BoujeeEnjinia1701/twinkit/cad/drawings/TWK-DWG-001.pdf

CONCEPT, NOT FOR FABRICATION | TwinKit · github.com/BoujeeEnjinia1701/twinkit

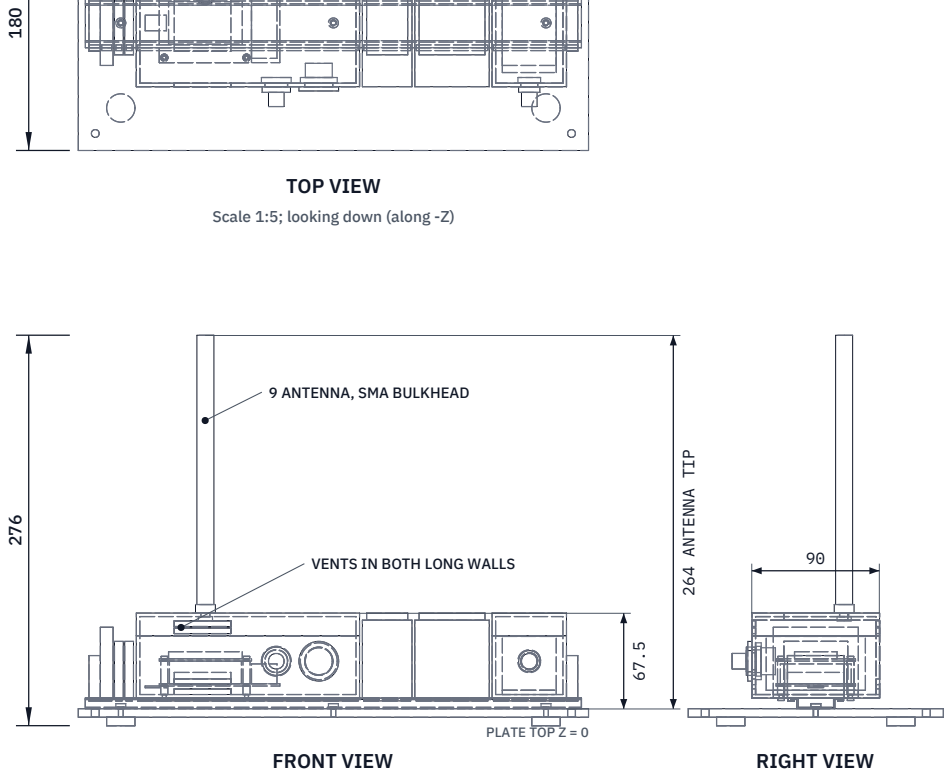
[picture p42: figure]
FRONT VIEW; TOP VIEW; Scale 1:5; looking down (along -Z); RIGHT VIEW; 264 ANTENNA TIP; 9 ANTENNA, SMA BULKHEAD; VENTS IN BOTH LONG WALLS; PLATE TOP Z = 0

Scale 1:5; looking at the front (along +Y)

Scale 1:5; looking at the right side (along -X)

360

331 RAIL USED (18.9 MODULES)

157.5 (9 MODULES)

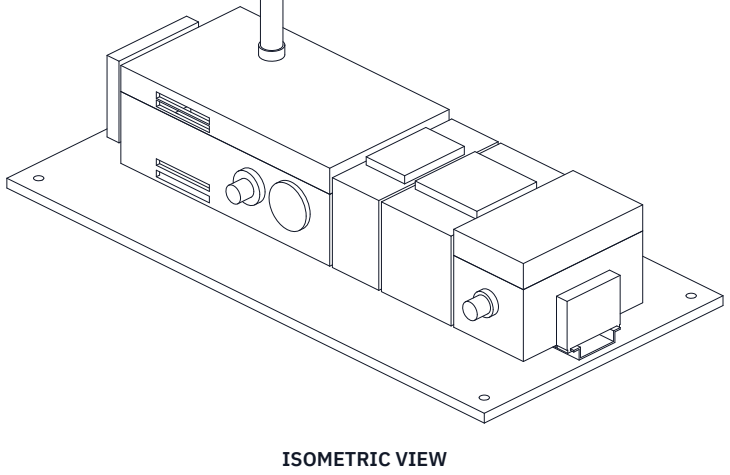
[picture p43: figure]
ISOMETRIC VIEW

Not to scale; seen from the front right and above, about 30 deg elevation

MAIN DIMENSIONS AND INTERFACES (MM)
TS35 x 7.5 rail, 350 long, on 3 M4 screws; module pitch 17.5
13 terminals, fuse | 3, 4 enclosure 9 mod | 10 DC-DC 2 mod | 11 UPS 3 mod
17 battery box 3 mod holding 12 pack (12.8 V, 1.5 Ah) | 18 end stops
Enclosure 157.5 x 90 x 60 above the rail; top 67.5 above the plate
Vents 640 mm2 low and high, 42 apart (TWK-CAL-001 F)
5 board 85 x 56 on 6 standoffs; 7 HAT on 16 standoffs
20 RJ45 coupler and cable glands in the -Y walls; 9 to 30 V DC in Plate 360 x 180 x 6 aluminium; omit in a cabinet
Third-angle; front view from -Y; X along the rail
REV | DESCRIPTION | DATE | BY
P1 | Preliminary GA for TRL 3 (from cad/src/model.py) | 2026-09-25 | AC
P2 | Layout and labels tidied | 2026-09-25 | AC
P3 | Constructable design: vents in long walls, battery box, end stops, fixings (TWK-DDR-003) | 2026-10-02 | AC
TWINKIT | github.com/BoujeeEnjinia1701/twinkit

## General arrangement, edge gateway

DRAWING NO.
TWK-DWG-001

REV
P3

SHEET
1 of 1

SIZE

## ANSI B

SCALE
1:5

UNITS
mm
PROJECTION | DATE
2026-10-02

DRAWN
Amish Chadha

MATERIAL / NOTES
Bought-in DIN modules per bom/bom.csv. PRELIMINARY, NOT FOR FABRICATION
Licensed CERN-OHL-S-2.0 · Design Molecule Lab · designmolecule.com | Generated from cad/src; do not edit by hand
