BoujeeEnjinia1701/twinkit/cad/drawings/TWK-DWG-101.pdf

### BUILD PLAN SKETCH, PLAN NOT YET BUILT TwinKit · github.com/BoujeeEnjinia1701/twinkit

FRONT VIEW
Scale 1:5; looking at the front (along +Y)

TOP VIEW
Scale 1:5; looking down (along -Z)

RIGHT VIEW
Scale 1:5; looking at the right side (along -X)

360

180 6

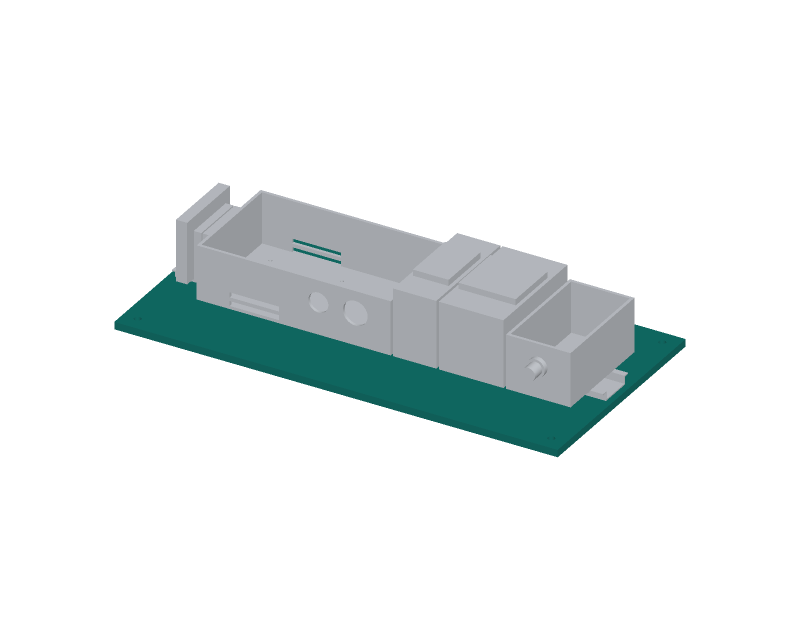
[picture p44: figure]

WHERE IT GOES
This part in colour, its neighbours in grey

HOW TO MAKE IT AND HOW IT FITS
Blank 360 x 180 x 6 mm. Cut square, file the edges, round the corners to about 3 mm. Scribe a centre line along the long side. Rail holes: three on the centre line, at the middle and 150 mm
each side of it. Drill 3.3 mm right through and tap M4.
Corner holes: four 5.5 mm holes, 12 mm in from each long and short edge, for screwing the plate to a wall or cabinet later.
Deburr every hole on both faces.
Underneath: four stick-on rubber feet, 20 mm across, centred
150 mm each side of the middle and 60 mm each side of the centre line. Fit: the rail lies on the centre line, held by three M4 x 6 mm
pan-head screws through its base into the tapped holes.
Check: an M4 screw runs into each hole by hand; the plate rocks
on none of its feet on a flat bench.
REV | DESCRIPTION | DATE | BY
P1 | Making sketch for the prototype build plan | 2026-10-02 | AC
TWINKIT | github.com/BoujeeEnjinia1701/twinkit

## TwinKit bench plate: making sketch

DRAWING NO.
TWK-DWG-101

REV
P1

SHEET
1 of 1

SIZE

## ANSI B

SCALE
1:5

UNITS
mm
PROJECTION | DATE
2026-10-02

DRAWN
Amish Chadha

MATERIAL / NOTES
Aluminium sheet 6 mm, 5083, 6082 or 6061 class
Licensed CERN-OHL-S-2.0 · Design Molecule Lab · designmolecule.com | Generated from cad/src; do not edit by hand
