BoujeeEnjinia1701/twinkit/cad/drawings/TWK-DWG-102.pdf

### BUILD PLAN SKETCH, PLAN NOT YET BUILT TwinKit · github.com/BoujeeEnjinia1701/twinkit

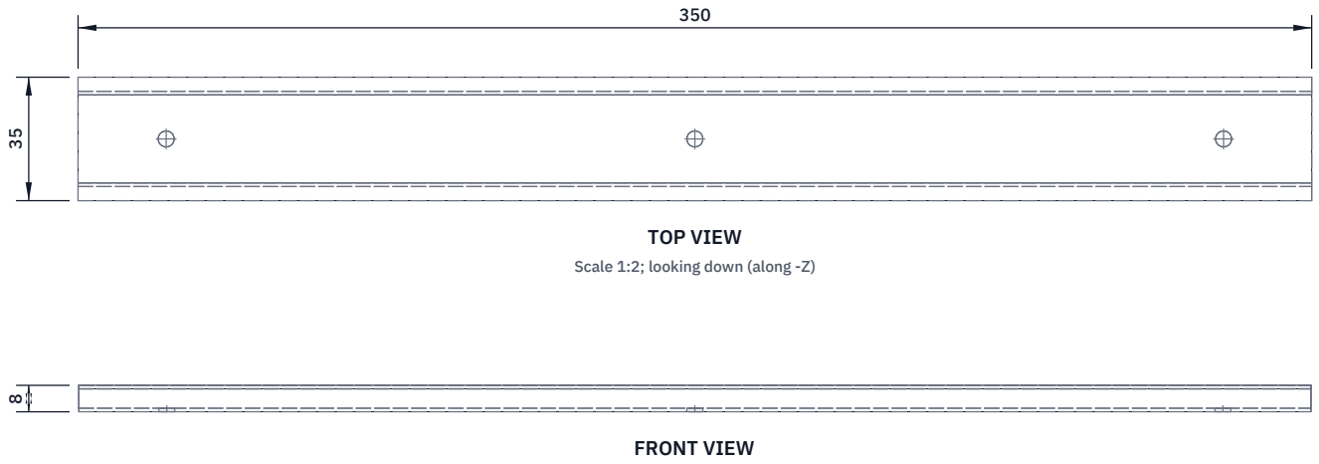
[picture p45: figure]
FRONT VIEW; TOP VIEW; Scale 1:2; looking down (along -Z)

Scale 1:2; looking at the front (along +Y)

RIGHT VIEW
Scale 1:2; looking at the right side (along -X)

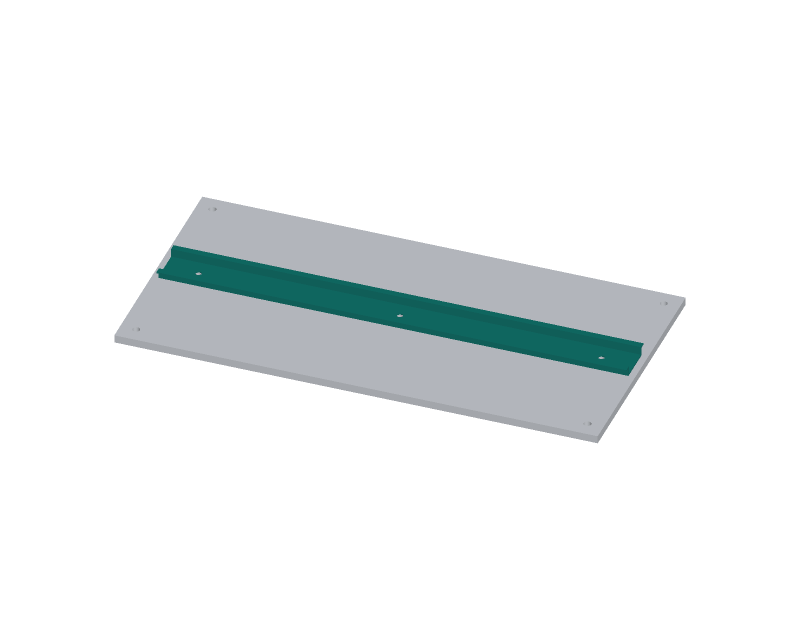
[picture p46: figure]

WHERE IT GOES
This part in colour, its neighbours in grey

HOW TO MAKE IT AND HOW IT FITS
Cut a 350 mm length of TS35 x 7.5 slotted top-hat rail with a hacksaw; file the cut ends square and remove every burr.
The rail is 35 mm wide across its top flanges, 7.5 mm high, with a 27 mm wide base that lies on the plate.
Holes: three, on the rail's centre line, at the middle and 150 mm each side. Where a slot already falls within 3 mm of a mark, use the slot; otherwise drill 4.5 mm through the base.
Fit: lay the rail on the plate's centre line, ends 5 mm in from the plate's short edges. Three M4 x 6 mm pan-head screws, snug. Every module clips over the two top flanges; the screw heads sit 3.9 mm below the modules, so nothing rubs.
Check: the rail lies flat along its length; a module clips on and slides along it from end to end without catching on a screw.
REV | DESCRIPTION | DATE | BY
P1 | Making sketch for the prototype build plan | 2026-10-02 | AC
TWINKIT | github.com/BoujeeEnjinia1701/twinkit

## TwinKit DIN rail: making sketch

DRAWING NO.
TWK-DWG-102

REV
P1

SHEET
1 of 1

SIZE

## ANSI B

SCALE
1:2

UNITS
mm
PROJECTION | DATE
2026-10-02

DRAWN
Amish Chadha

MATERIAL / NOTES
TS35 x 7.5 top-hat rail, slotted, steel or aluminium
Licensed CERN-OHL-S-2.0 · Design Molecule Lab · designmolecule.com | Generated from cad/src; do not edit by hand
