BoujeeEnjinia1701/twinkit/cad/drawings/TWK-DWG-103.pdf

### BUILD PLAN SKETCH, PLAN NOT YET BUILT TwinKit · github.com/BoujeeEnjinia1701/twinkit

FRONT VIEW
Scale 1:2; looking at the front (along +Y)

TOP VIEW
Scale 1:2; looking down (along -Z)

RIGHT VIEW
Scale 1:2; looking at the right side (along -X)

158

90 46

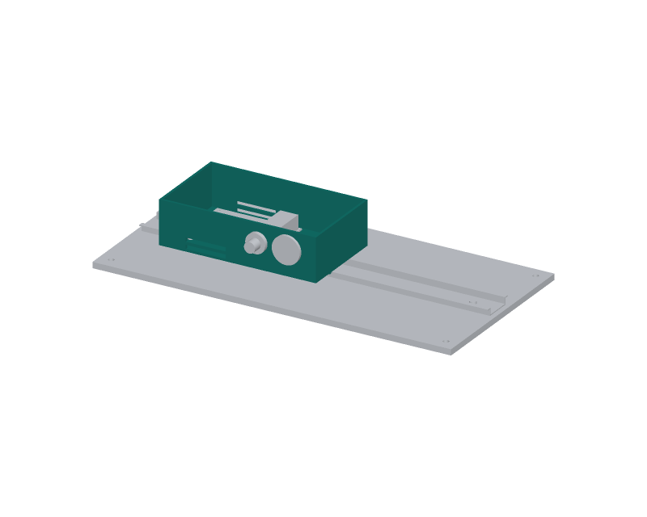
[picture p47: figure]

WHERE IT GOES
This part in colour, its neighbours in grey

HOW TO MAKE IT AND HOW IT FITS
The front is the long wall that will face you on the bench; the antenna sits toward the back. Mark the front before cutting. Vent slots: two slots 40 x 4 mm in each long wall, centred 32 mm left of the middle, 2.5 to 6.5 and 9.5 to 13.5 mm above the outside of the floor. Chain drill 3.5 mm and file to the line.
Front wall, 26 mm above the outside of the floor: a 20 mm hole 50 mm right of the middle (network coupler) and a 16.2 mm hole 20 mm right of the middle (power gland). Step drill, light pressure. Floor: four 2.7 mm holes for the computer: 58 mm apart along the base and 49 mm apart across it, the left pair 59 mm and the right pair 1 mm left of the middle. Use the maker's bosses if it has them. Tape the faces first; no solvents; deburr inside and out.
Check: lay the computer on the floor; its holes line up with yours.
REV | DESCRIPTION | DATE | BY
P1 | Making sketch for the prototype build plan | 2026-10-02 | AC
TWINKIT | github.com/BoujeeEnjinia1701/twinkit

## TwinKit gateway enclosure base: cutting and drilling sketch

DRAWING NO.
TWK-DWG-103

REV
P1

SHEET
1 of 1

SIZE

## ANSI B

SCALE
1:2

UNITS
mm
PROJECTION | DATE
2026-10-02

DRAWN
Amish Chadha

MATERIAL / NOTES
Bought 9-module DIN enclosure base, polycarbonate, 157.5 x 90 x 44 mm
Licensed CERN-OHL-S-2.0 · Design Molecule Lab · designmolecule.com | Generated from cad/src; do not edit by hand
