BoujeeEnjinia1701/twinkit/cad/drawings/TWK-DWG-104.pdf

### BUILD PLAN SKETCH, PLAN NOT YET BUILT TwinKit · github.com/BoujeeEnjinia1701/twinkit

FRONT VIEW
Scale 1:2; looking at the front (along +Y)

TOP VIEW
Scale 1:2; looking down (along -Z)

RIGHT VIEW
Scale 1:2; looking at the right side (along -X)

158

90 16

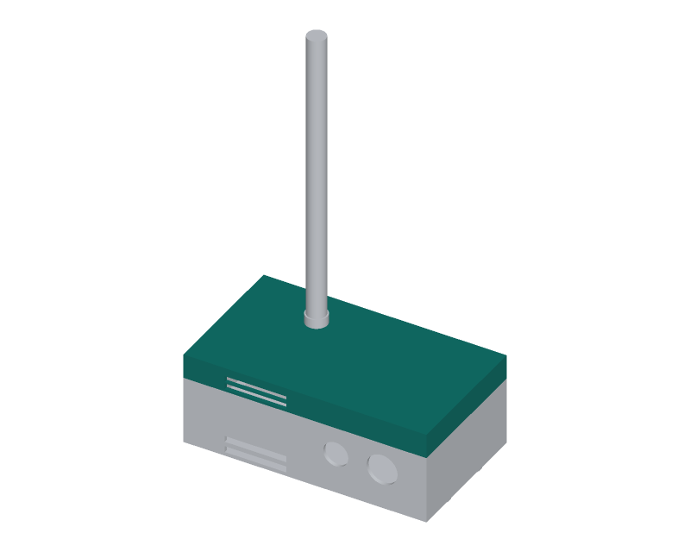
[picture p48: figure]

WHERE IT GOES
This part in colour, its neighbours in grey

HOW TO MAKE IT AND HOW IT FITS
Antenna hole: 6.5 mm through the top, 30 mm left of the middle and 20 mm behind the centre line (toward the back wall).
Pilot 3 mm, then step drill; check the size on the bulkhead's datasheet before the last step.
Vent slots: two slots 40 x 4 mm in each long wall, in line with the base's slots, 1.5 to 5.5 and 6.5 to 10.5 mm above the cover's lower edge. Skip any the maker has already moulded.
Deburr; clean with water and mild soap only.
Fit: the bulkhead goes in from above, flange and washer on the outside, nut inside. The cover then closes onto the base with
the maker's clips or screws.
Check: the bulkhead nut clears the concentrator HAT by 20 mm when the cover is closed.
REV | DESCRIPTION | DATE | BY
P1 | Making sketch for the prototype build plan | 2026-10-02 | AC
TWINKIT | github.com/BoujeeEnjinia1701/twinkit

## TwinKit gateway enclosure cover: drilling sketch

DRAWING NO.
TWK-DWG-104

REV
P1

SHEET
1 of 1

SIZE

## ANSI B

SCALE
1:2

UNITS
mm
PROJECTION | DATE
2026-10-02

DRAWN
Amish Chadha

MATERIAL / NOTES
Bought cover for the 9-module enclosure, clear or tinted polycarbonate
Licensed CERN-OHL-S-2.0 · Design Molecule Lab · designmolecule.com | Generated from cad/src; do not edit by hand
