BoujeeEnjinia1701/twinkit/cad/drawings/TWK-DWG-105.pdf

### BUILD PLAN SKETCH, PLAN NOT YET BUILT TwinKit · github.com/BoujeeEnjinia1701/twinkit

FRONT VIEW
Scale 1:2; looking at the front (along +Y)

TOP VIEW
Scale 1:2; looking down (along -Z)

RIGHT VIEW
Scale 1:2; looking at the right side (along -X)

52

90 46

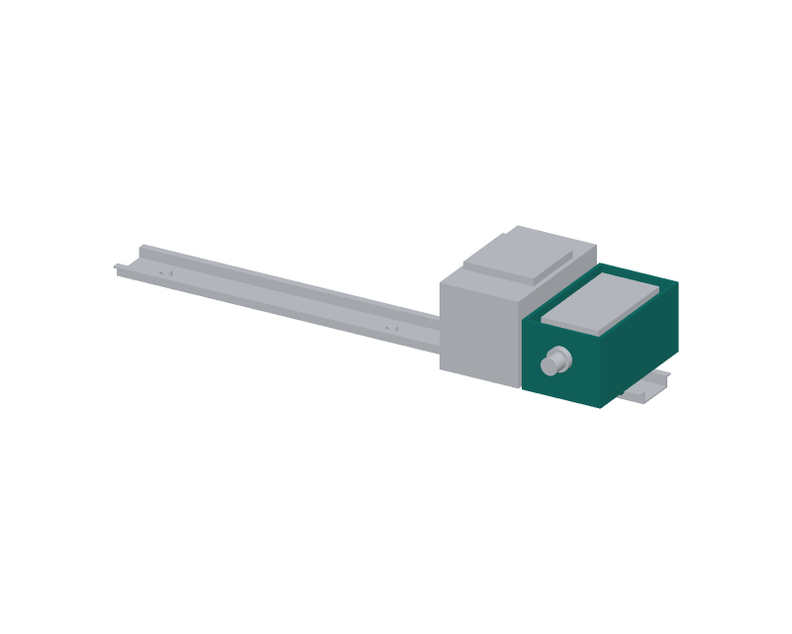
[picture p49: figure]

WHERE IT GOES
This part in colour, its neighbours in grey

HOW TO MAKE IT AND HOW IT FITS
One 12.2 mm hole in the front wall, on the middle of the wall, 26 mm above the outside of the floor, for the M12 gland that
the pack lead passes through. Pilot 3 mm, then step drill.
Deburr inside and out.
Inside: a hook-and-loop pad 38 x 60 mm stuck to the middle of the floor; its mate goes on the pack's underside.
The pack (38 x 70 x 38 mm at most) lies on the pad, long side front to back, 3.5 mm clear of the gland nut.
Fit: the gland goes in from outside, seal outside, nut inside. Check: the pack sits on the pad with its lead reaching the gland without strain, and the cover closes without touching it.
REV | DESCRIPTION | DATE | BY
P1 | Making sketch for the prototype build plan | 2026-10-02 | AC
TWINKIT | github.com/BoujeeEnjinia1701/twinkit

## TwinKit battery box base: drilling sketch

DRAWING NO.
TWK-DWG-105

REV
P1

SHEET
1 of 1

SIZE

## ANSI B

SCALE
1:2

UNITS
mm
PROJECTION | DATE
2026-10-02

DRAWN
Amish Chadha

MATERIAL / NOTES
Bought 3-module DIN enclosure base, polycarbonate, 52.5 x 90 x 44 mm
Licensed CERN-OHL-S-2.0 · Design Molecule Lab · designmolecule.com | Generated from cad/src; do not edit by hand
