BoujeeEnjinia1701/twinkit/media/card.png

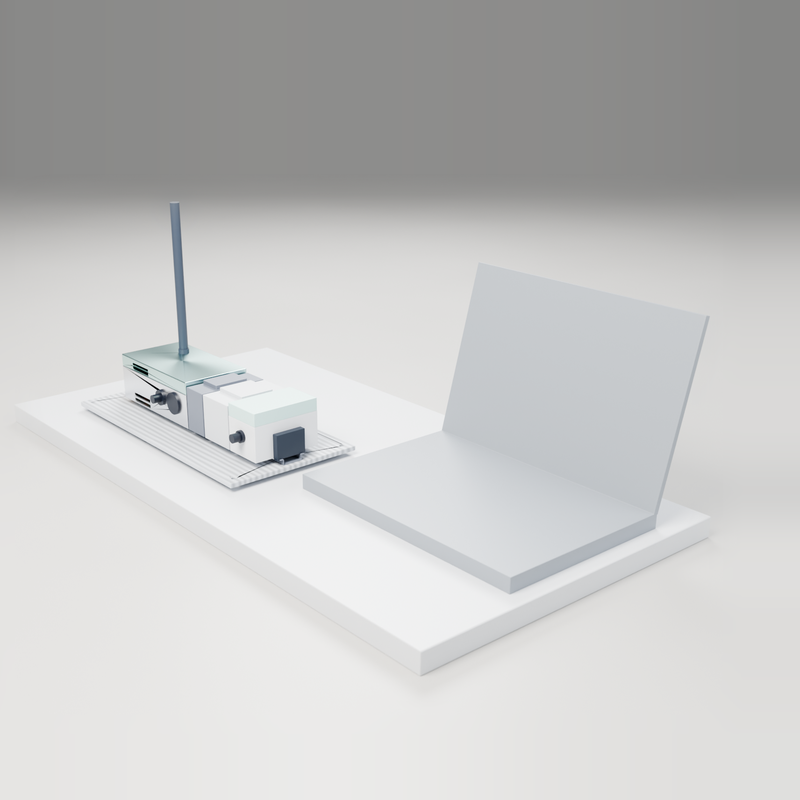
media/card.png
