BoujeeEnjinia1701/twinkit/media/social-preview.png

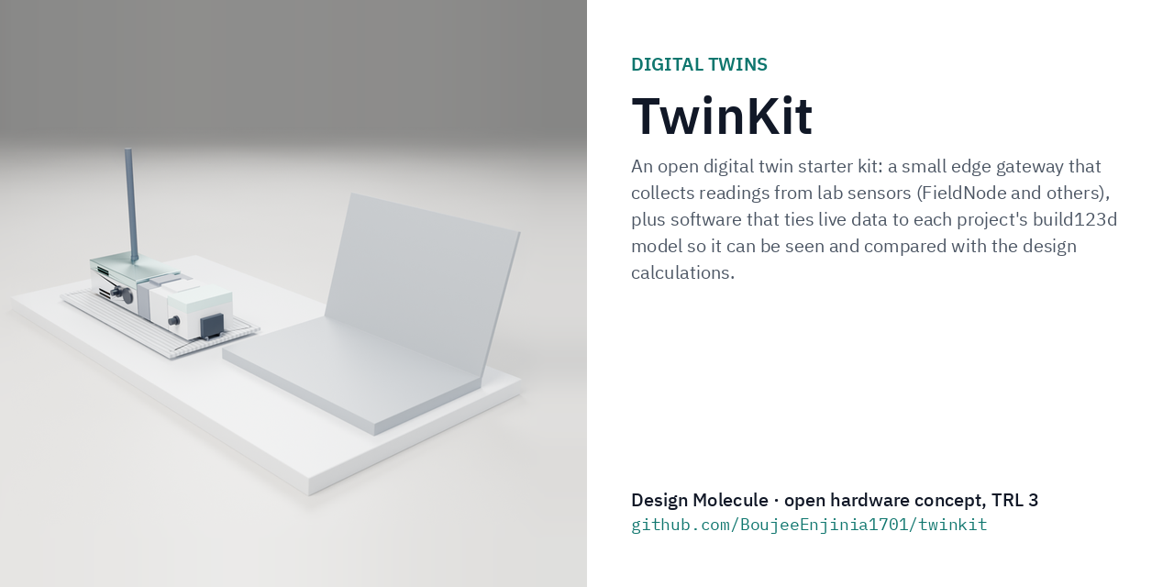
media/social-preview.png
